cuspaceflight/spalax/firmware/src/adis16405.h

#ifndef ADIS16405_H
#define ADIS16405_H

#include "ch.h"
#include "hal.h"

#if BUILD_ADIS

void adis16405_thread(void *arg);


/* Interrupt callbacks for EXTI. */
void adis16405_wakeup(EXTDriver *extp, expchannel_t channel);

#endif

#endif /* ADIS16405_H */
