cuspaceflight/spalax/firmware/src/adis16405-reg.h

#ifndef ADIS16405_REG_H
#define ADIS16405_REG_H

enum {
    ADIS16405_REG_FLASH_CNT = 0x00,
    ADIS16405_REG_SUPPLY_OUT = 0x02,
    ADIS16405_REG_XGYRO_OUT = 0x04,
    ADIS16405_REG_YGYRO_OUT = 0x06,
    ADIS16405_REG_ZGYRO_OUT = 0x08,
    ADIS16405_REG_XACCL_OUT = 0x0A,
    ADIS16405_REG_YACCL_OUT = 0x0C,
    ADIS16405_REG_ZACCL_OUT = 0x0E,
    ADIS16405_REG_XMAGN_OUT = 0x10,
    ADIS16405_REG_YMAGN_OUT = 0x12,
    ADIS16405_REG_ZMAGN_OUT = 0x14,
    ADIS16405_REG_TEMP_OUT = 0x16,
    ADIS16405_REG_AUX_ADC = 0x18,
    ADIS16405_REG_XGYRO_OFF = 0x1A,
    ADIS16405_REG_YGYRO_OFF = 0x1C,
    ADIS16405_REG_ZGYRO_OFF = 0x1E,
    ADIS16405_REG_XACCL_OFF = 0x20,
    ADIS16405_REG_YACCL_OFF = 0x22,
    ADIS16405_REG_ZACCL_OFF = 0x24,
    ADIS16405_REG_XMAGN_HIF = 0x26,
    ADIS16405_REG_YMAGN_HIF = 0x28,
    ADIS16405_REG_ZMAGN_HIF = 0x2A,
    ADIS16405_REG_XMAGN_SIF = 0x2C,
    ADIS16405_REG_YMAGN_SIF = 0x2E,
    ADIS16405_REG_ZMAGN_SIF = 0x30,
    ADIS16405_REG_GPIO_CTRL = 0x32,
    ADIS16405_REG_MSC_CTRL = 0x34,
    ADIS16405_REG_SMPL_PRD = 0x36,
    ADIS16405_REG_SENS_AVG = 0x38,
    ADIS16405_REG_SLP_CNT = 0x3A,
    ADIS16405_REG_DIAG_STAT = 0x3C,
    ADIS16405_REG_GLOB_CMD = 0x3E,
    ADIS16405_REG_ALM_MAG1 = 0x40,
    ADIS16405_REG_ALM_MAG2 = 0x42,
    ADIS16405_REG_ALM_SMPL1 = 0x44,
    ADIS16405_REG_ALM_SMPL2 = 0x46,
    ADIS16405_REG_ALM_CTRL = 0x48,
    ADIS16405_REG_AUX_DAC = 0x4A,
    ADIS16405_REG_PRODUCT_ID = 0x55,

    ADIS16405_PRODUCT_ID = 0x4105
};

#endif
