cuspaceflight/spalax/firmware/src/mpu9250.h

#ifndef MPU9250_H
#define MPU9250_H

#include "ch.h"
#include "hal.h"

void mpu9250_thread(void *arg);

/* Interrupt callbacks for EXTI. */
void mpu9250_wakeup(EXTDriver *extp, expchannel_t channel);

#endif /* MPU9250_H */
